monome/norns-shield/images/ns-kit-built.jpg

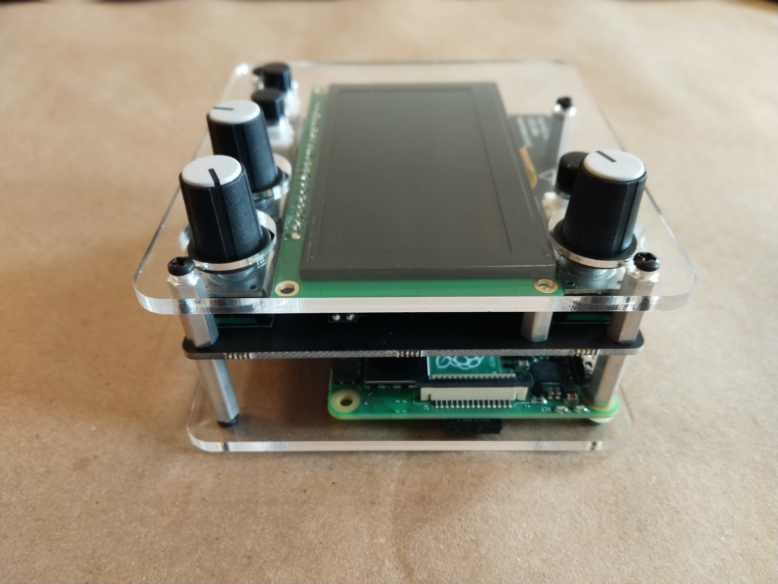
images/ns-kit-built.jpg
