monome/norns-shield/images/assembly/ns-0.jpg

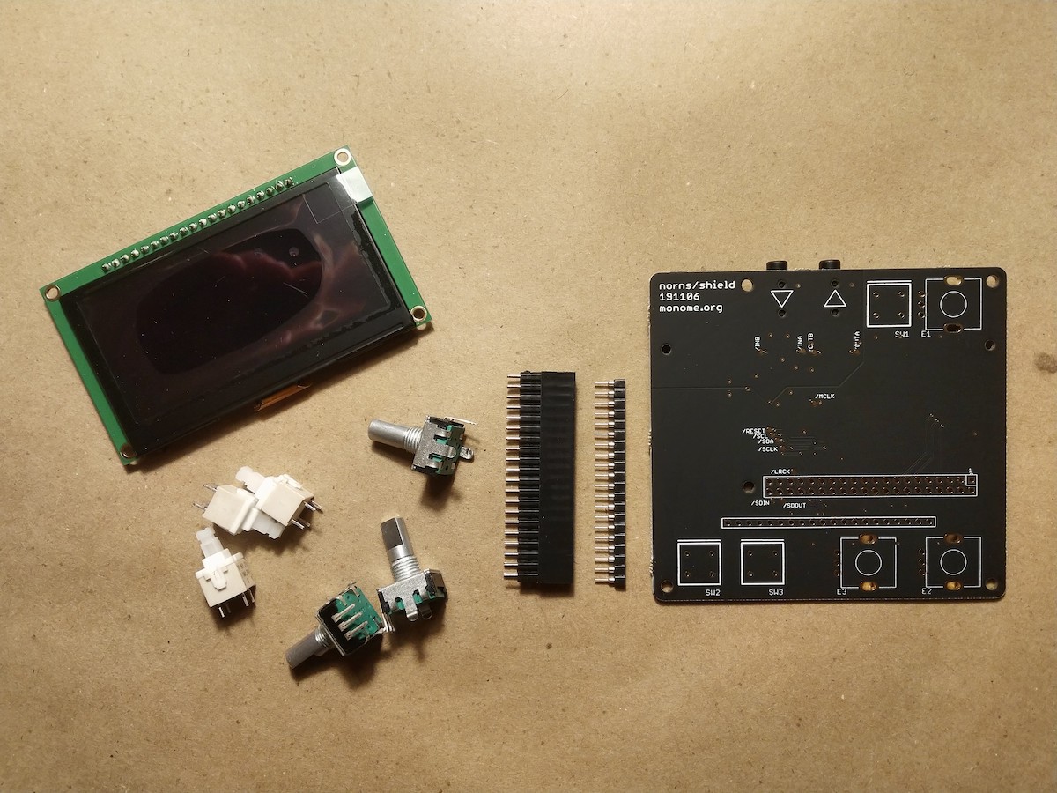
images/assembly/ns-0.jpg
