monome/norns-shield/images/assembly/ns-1.jpg

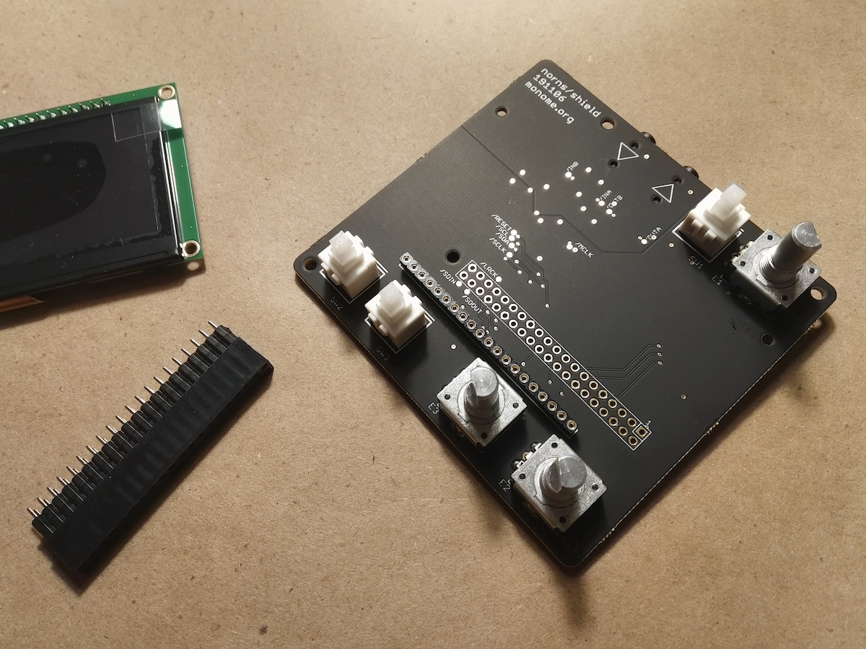
images/assembly/ns-1.jpg
