monome/norns-shield/images/assembly/ns-2.jpg

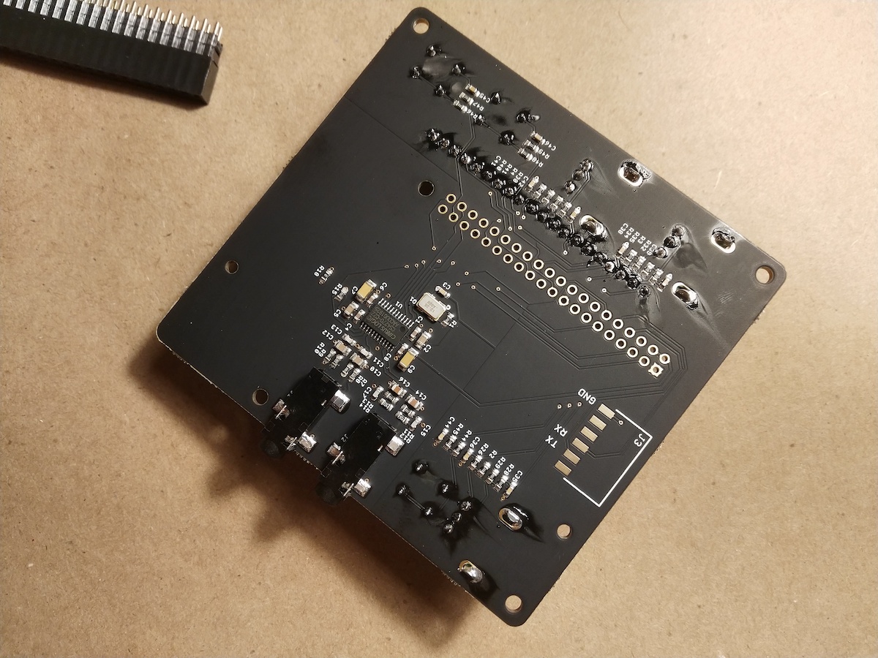
images/assembly/ns-2.jpg
