monome/norns-shield/images/assembly/ns-3.jpg

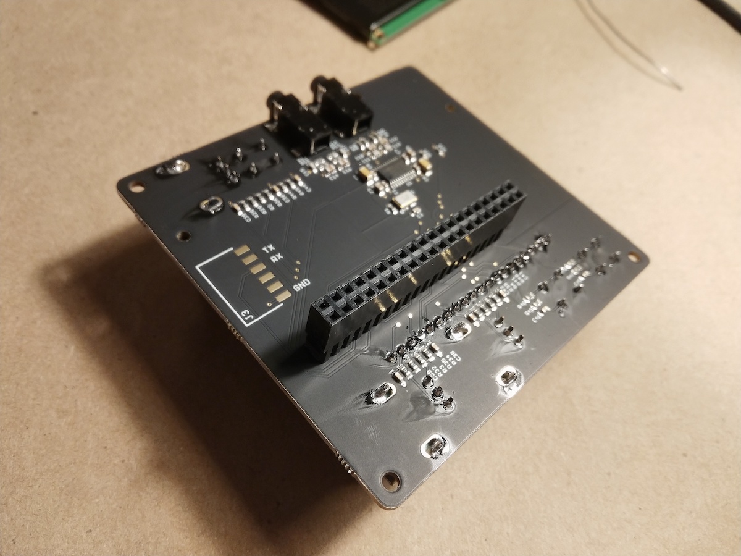
images/assembly/ns-3.jpg
