monome/norns-shield/images/assembly/ns-4.jpg

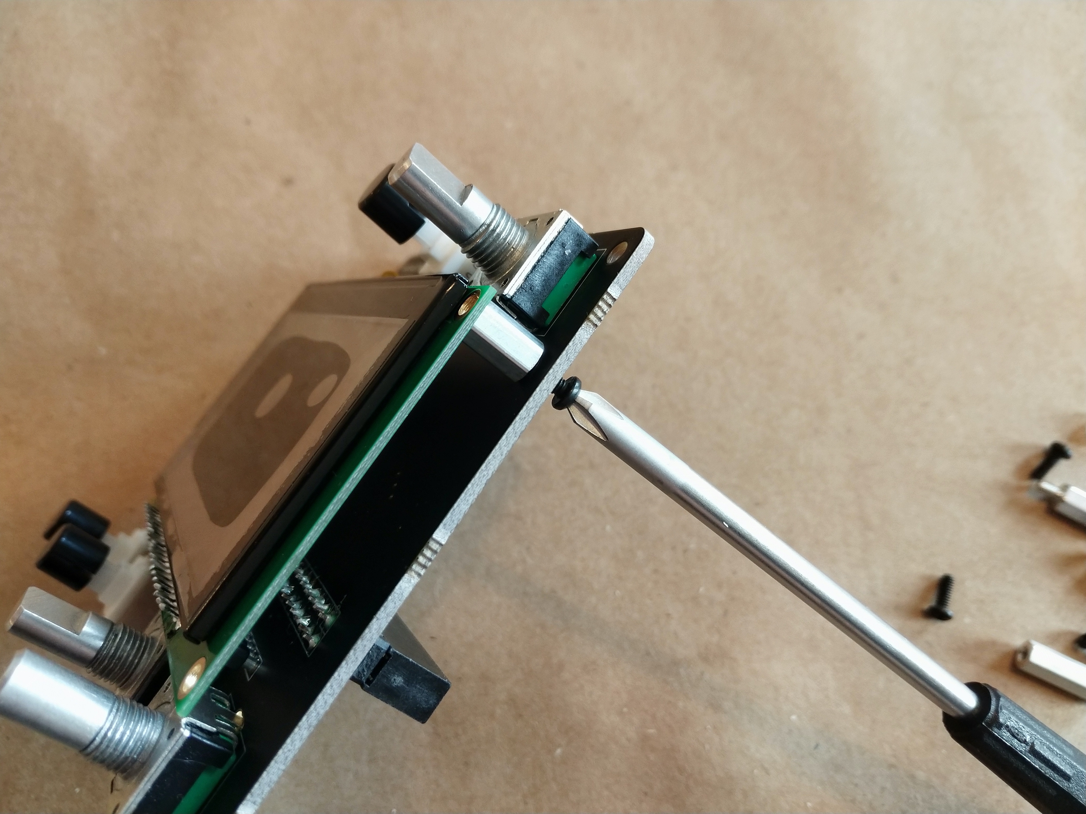
images/assembly/ns-4.jpg
