monome/norns-shield/images/assembly/ns-6.jpg

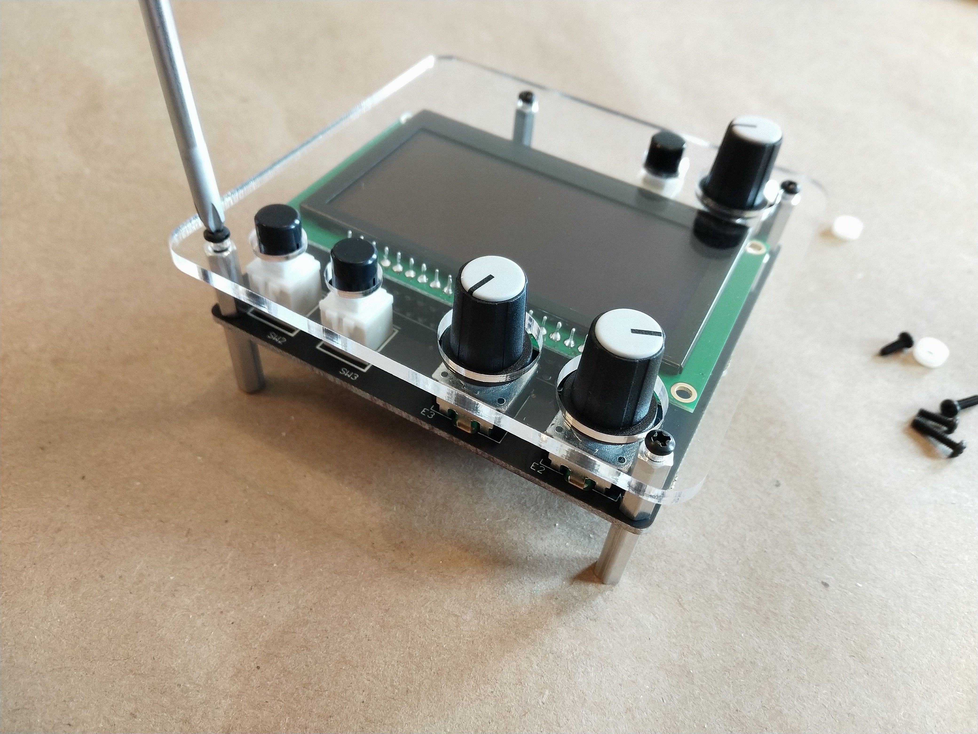
images/assembly/ns-6.jpg
