monome/norns-shield/images/assembly/ns-7.jpg

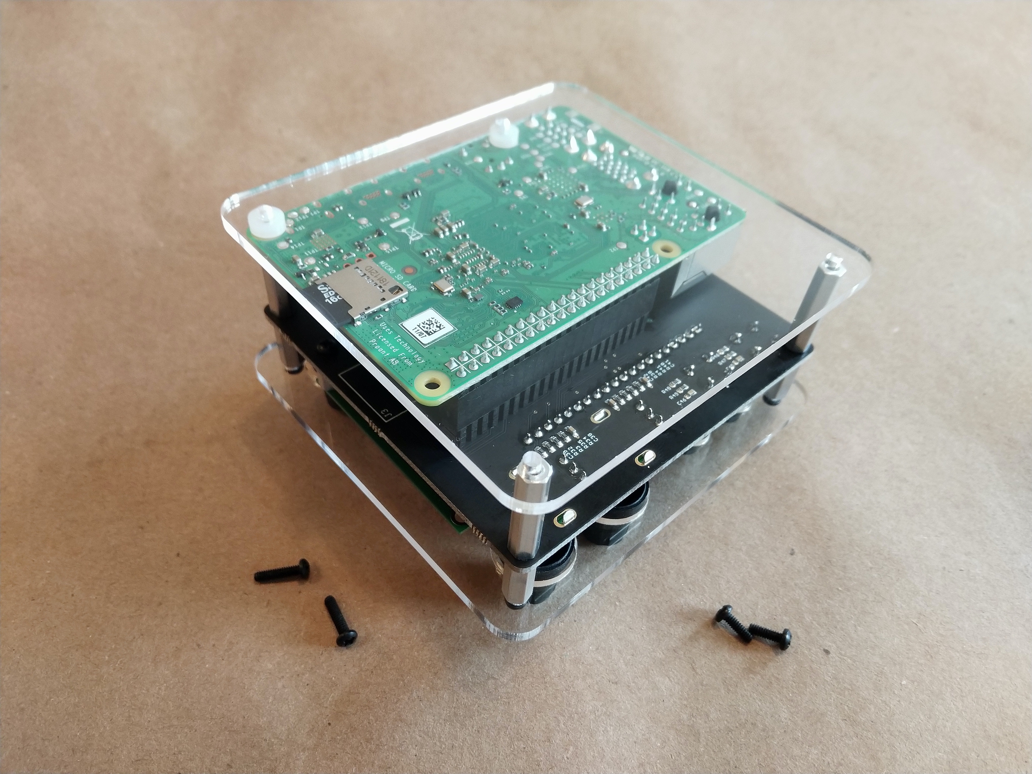
images/assembly/ns-7.jpg
